RetroLoom/Super-Wave-Blaster/Images/GPM02_MDF/CLK/SP_A_SNES-UN316642987-Toslink_CLK_APU.png

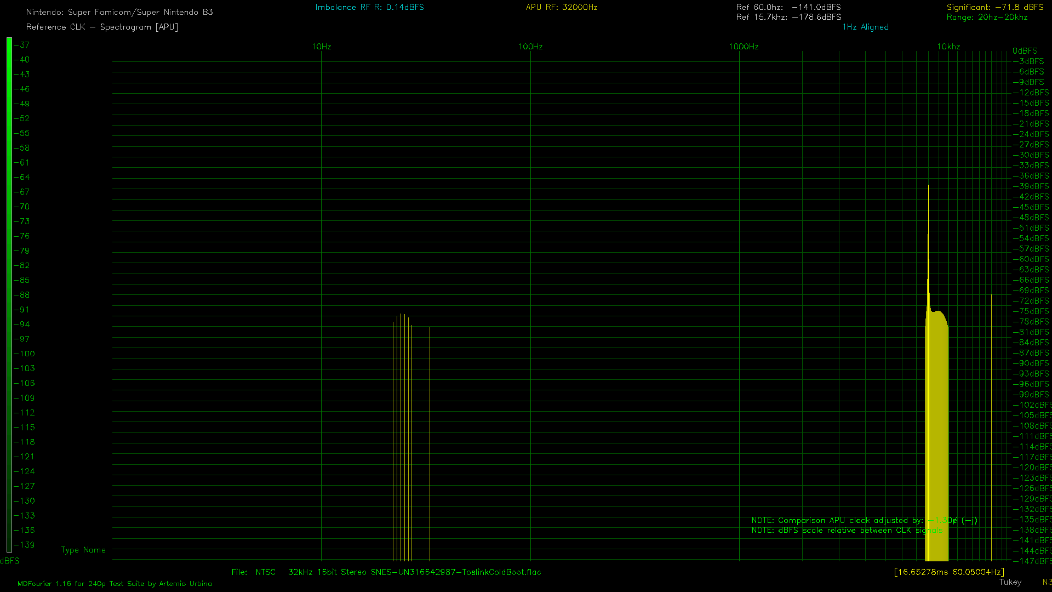
Images/GPM02_MDF/CLK/SP_A_SNES-UN316642987-Toslink_CLK_APU.png
