RetroLoom/Super-Wave-Blaster/Images/GPM02_MDF/CLK/SP_B_SWB GPM02 1UF OPA 44k_CLK_APU.png

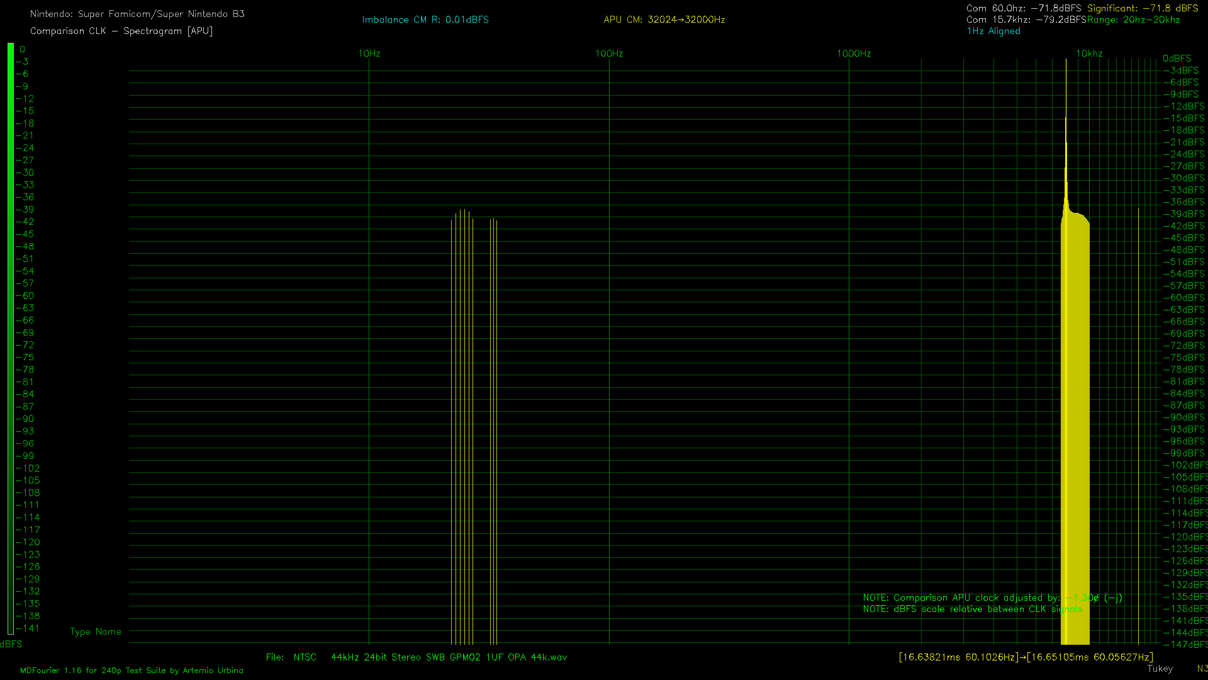
Images/GPM02_MDF/CLK/SP_B_SWB GPM02 1UF OPA 44k_CLK_APU.png
