RetroLoom/Super-Wave-Blaster/Images/GPM02_MDF/MISSING-A-T_SP_SNES-UN316642987-Toslink_S.png

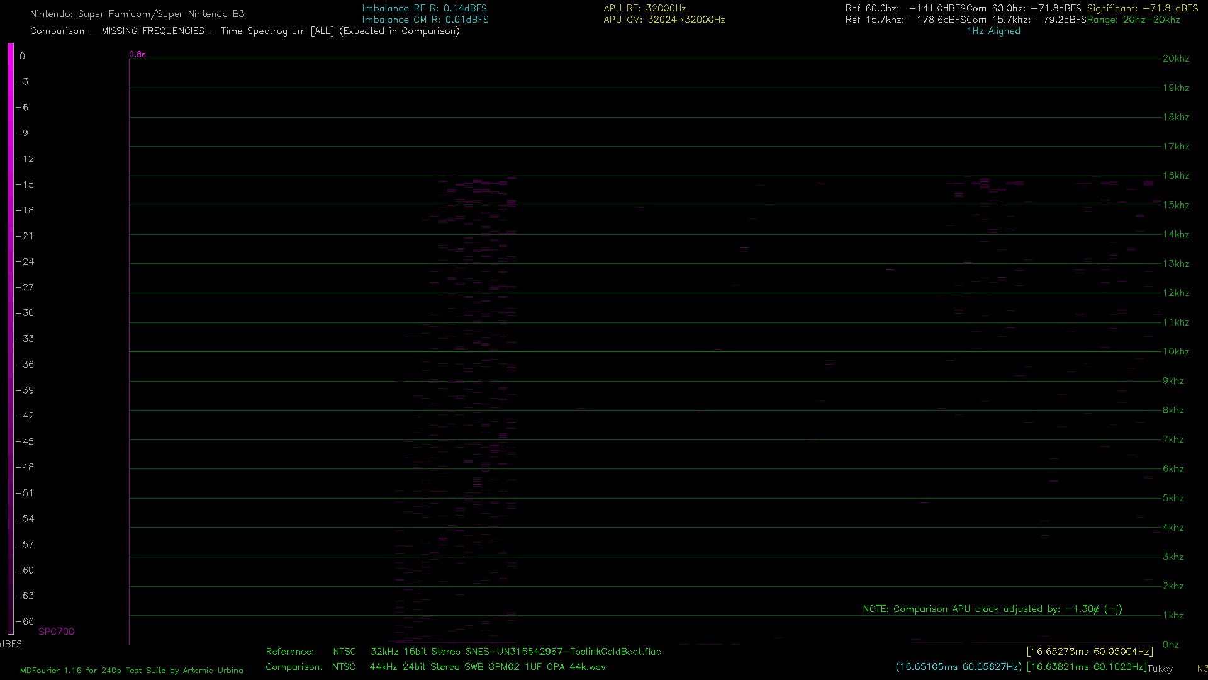
Images/GPM02_MDF/MISSING-A-T_SP_SNES-UN316642987-Toslink_S.png
