RetroLoom/Super-Wave-Blaster/Images/GPM02_MDF/MISSING-EXTRA_T_SP_SWB GPM02 1UF OPA 44k_S.png

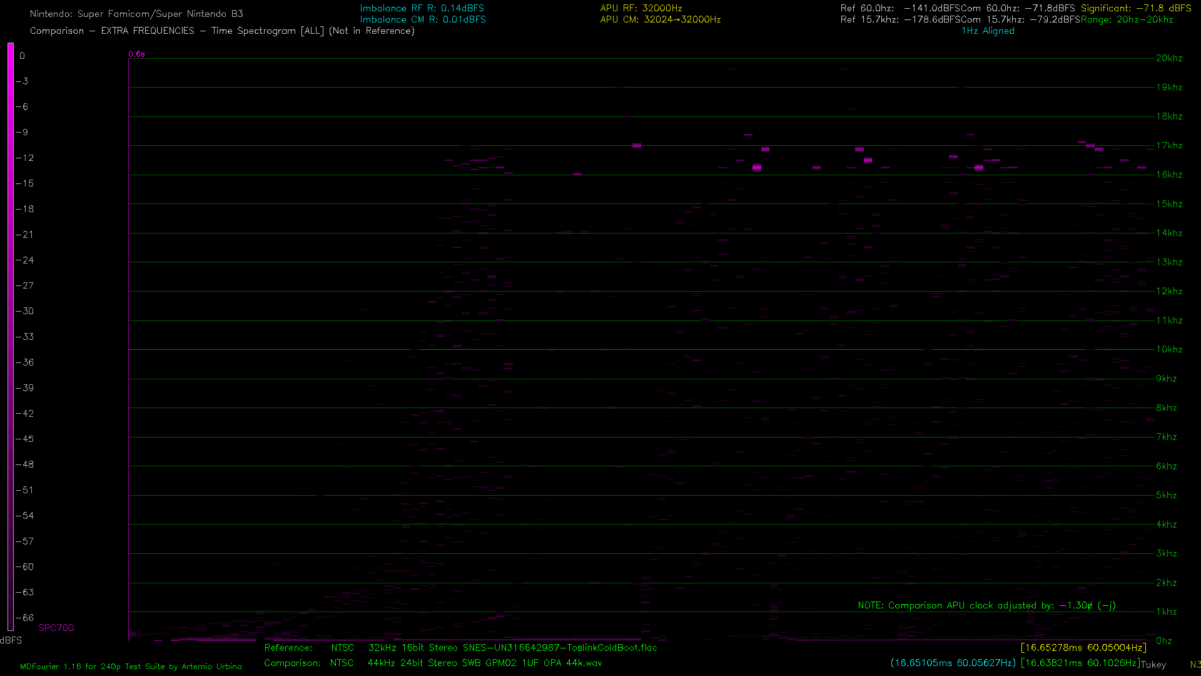
Images/GPM02_MDF/MISSING-EXTRA_T_SP_SWB GPM02 1UF OPA 44k_S.png
