RetroLoom/Super-Wave-Blaster/Images/GPM02_MDF/MissingAndExtra/MISSING-A-T_SP_SNES-UN316642987-Toslink_r.png

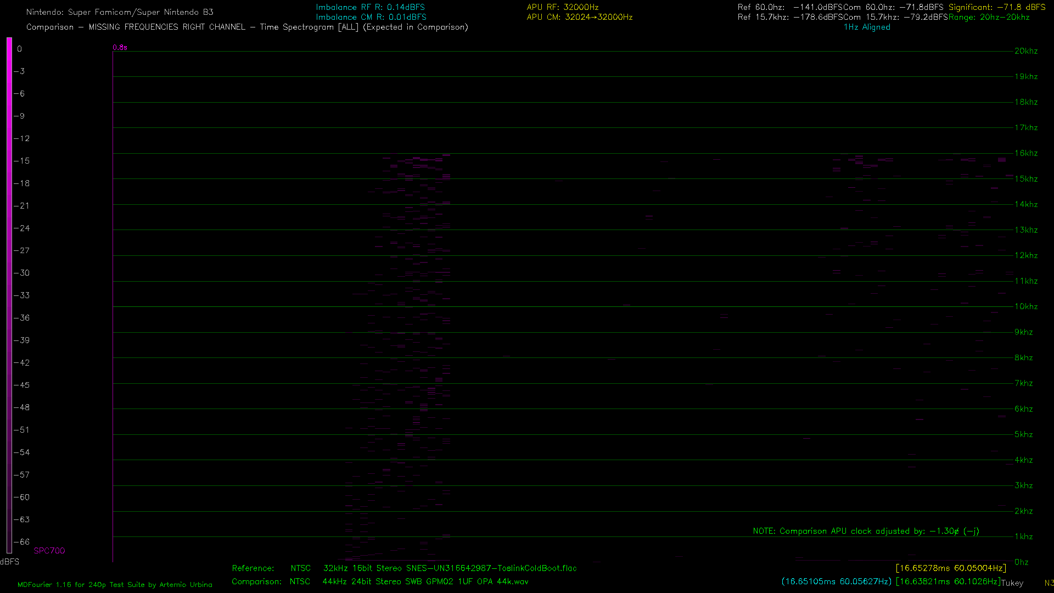
Images/GPM02_MDF/MissingAndExtra/MISSING-A-T_SP_SNES-UN316642987-Toslink_r.png
