RetroLoom/Super-Wave-Blaster/Images/GPM02_MDF/MissingAndExtra/MISSING-EXTRA_T_SP_SWB GPM02 1UF OPA 44k_l.png

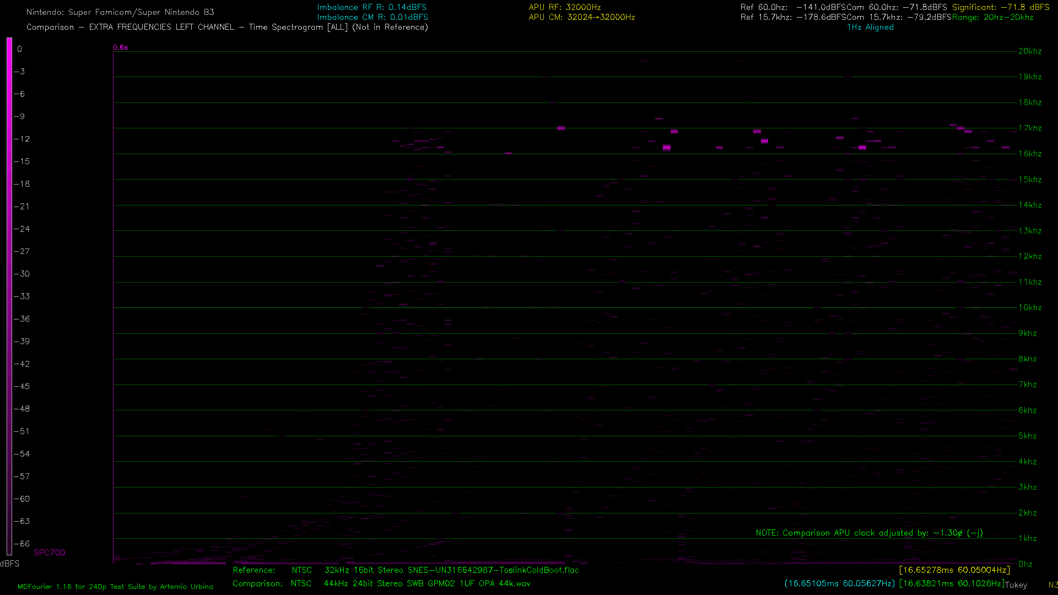
Images/GPM02_MDF/MissingAndExtra/MISSING-EXTRA_T_SP_SWB GPM02 1UF OPA 44k_l.png
