RetroLoom/Super-Wave-Blaster/Images/GPM02_MDF/NF__SNES-UN316642987-Toslink_vs_SWB_GPM02_1UF_OPA_44k_0000_-1Silence_AVG_.png

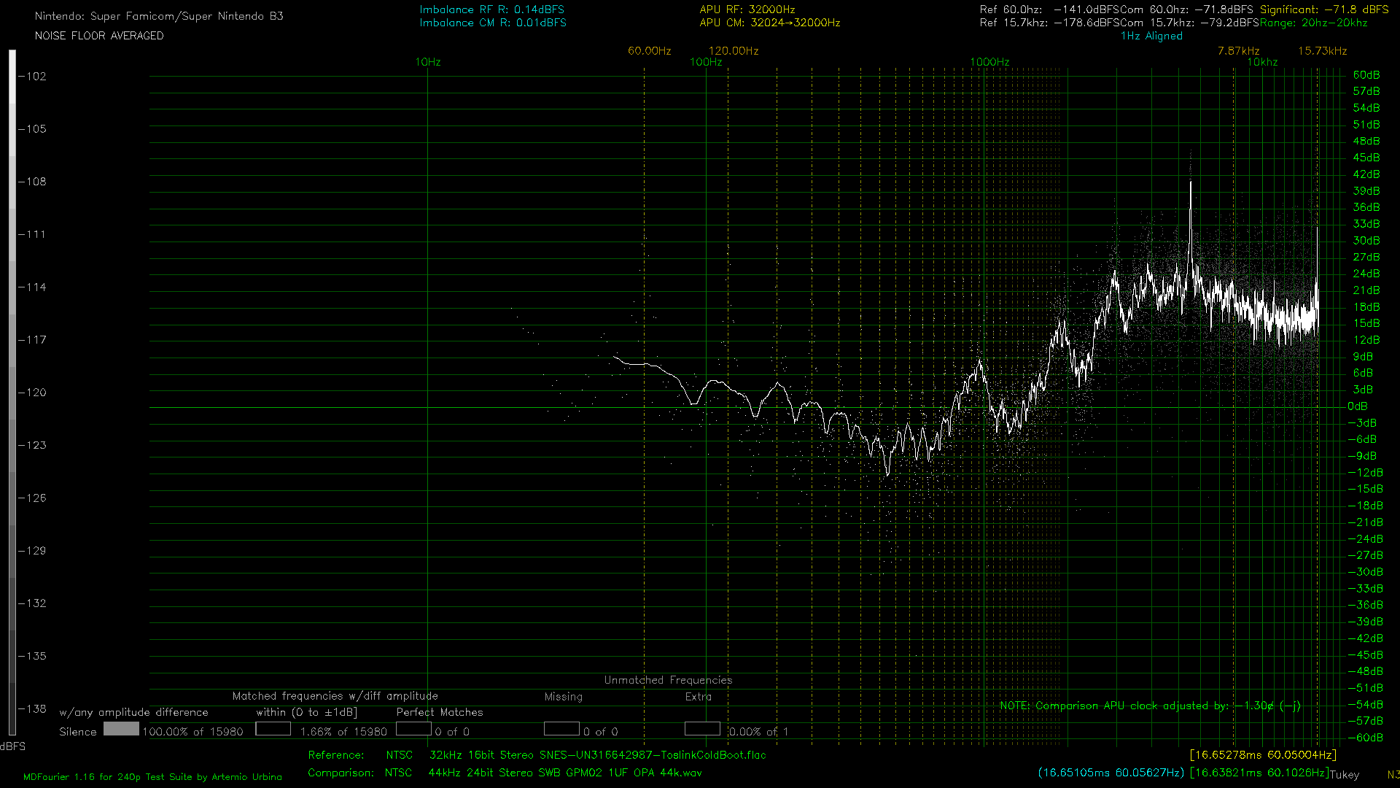
Images/GPM02_MDF/NF__SNES-UN316642987-Toslink_vs_SWB_GPM02_1UF_OPA_44k_0000_-1Silence_AVG_.png
