RetroLoom/Super-Wave-Blaster/Images/GPM02_MDF/NF_SP_A_SNES-UN316642987-Toslink_-1Silence.png

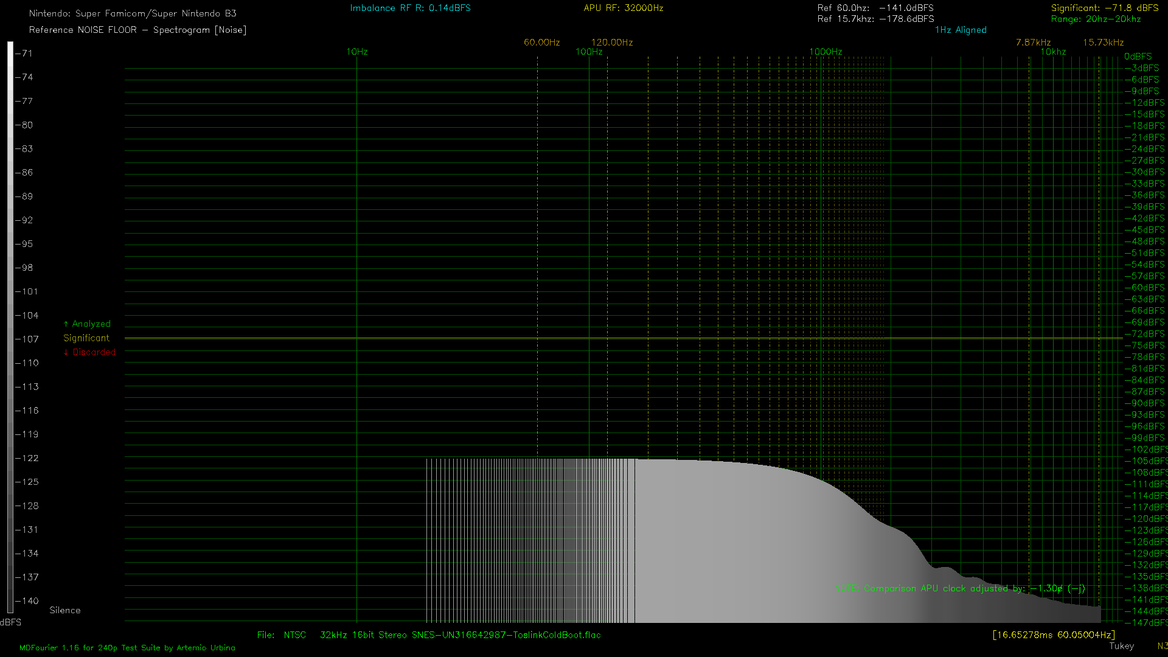
Images/GPM02_MDF/NF_SP_A_SNES-UN316642987-Toslink_-1Silence.png
