RetroLoom/Super-Wave-Blaster/Images/GPM02_MDF/NF_SP_B_SWB GPM02 1UF OPA 44k_-1Silence.png

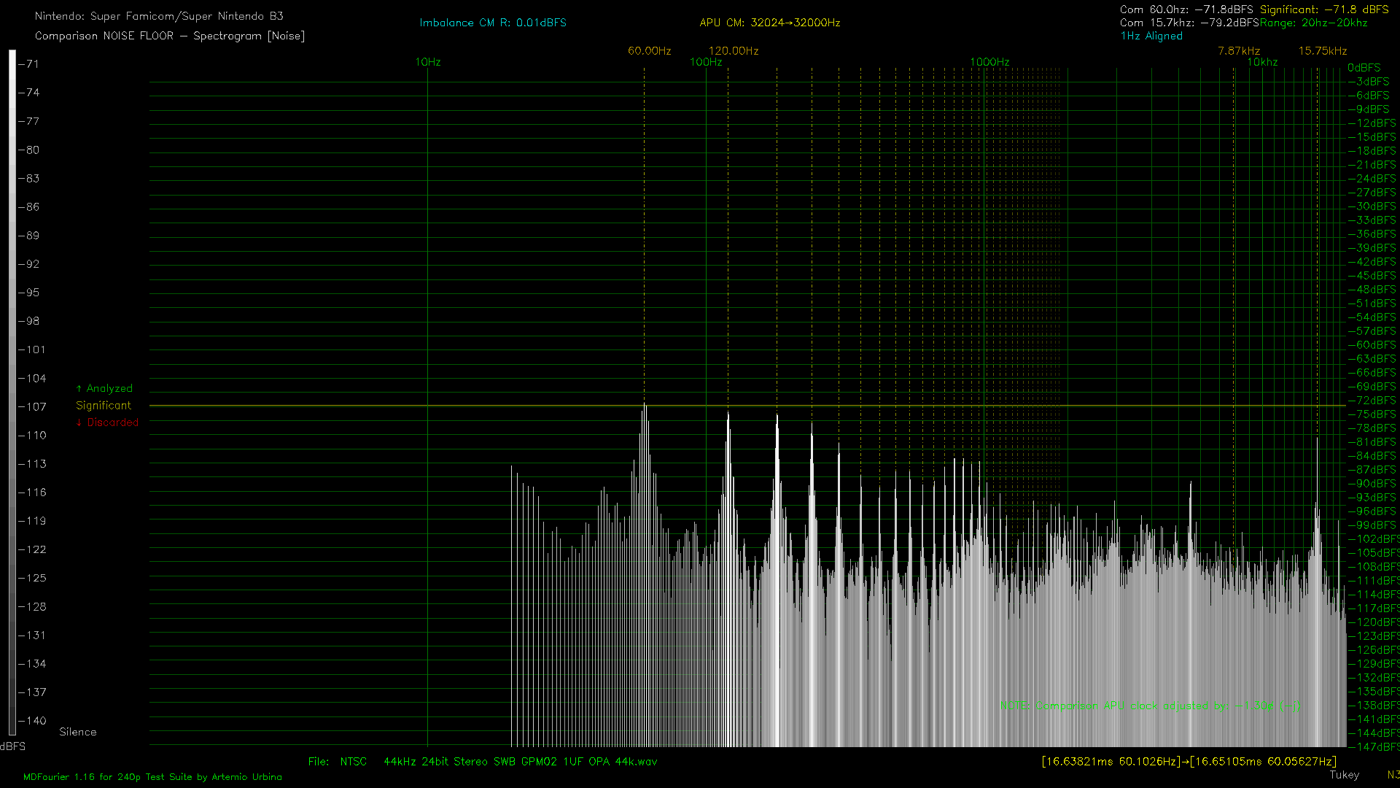
Images/GPM02_MDF/NF_SP_B_SWB GPM02 1UF OPA 44k_-1Silence.png
