RetroLoom/Super-Wave-Blaster/Images/GPM02_MDF/Phase/PHASE_DIFF_SNES-UN316642987-Toslink_vs_SWB_GPM02_1UF_OPA_44k_0000_01SPC700_r.png

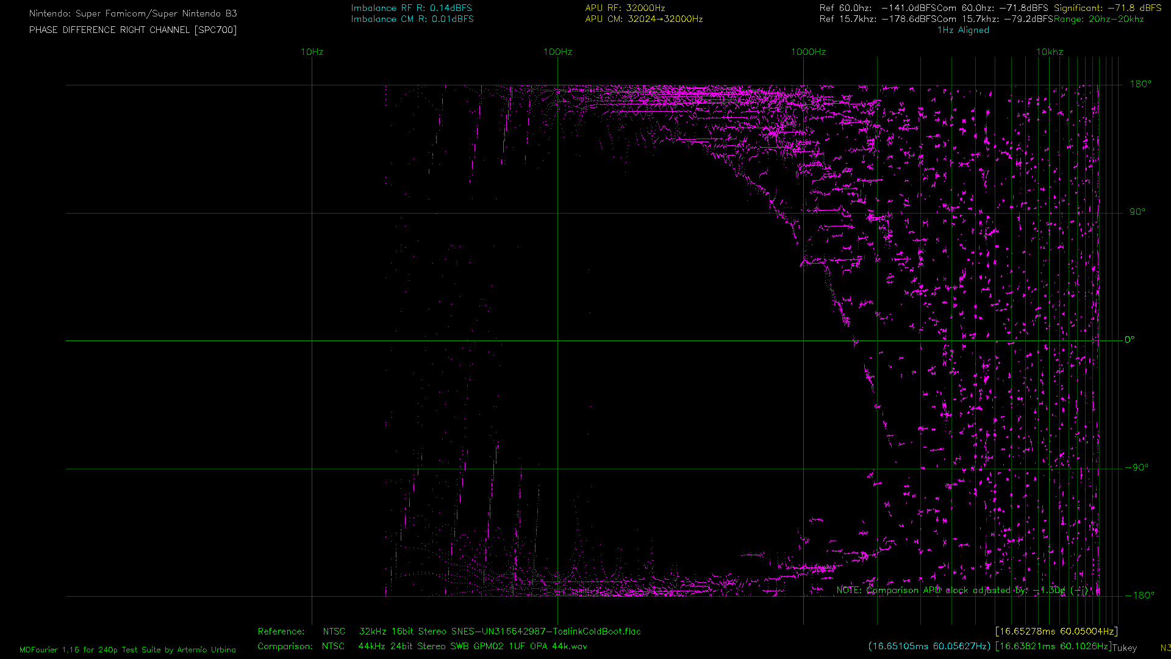
Images/GPM02_MDF/Phase/PHASE_DIFF_SNES-UN316642987-Toslink_vs_SWB_GPM02_1UF_OPA_44k_0000_01SPC700_r.png
