RetroLoom/Super-Wave-Blaster/Images/GPM02_MDF/T_SP_A_SNES-UN316642987-Toslink.png

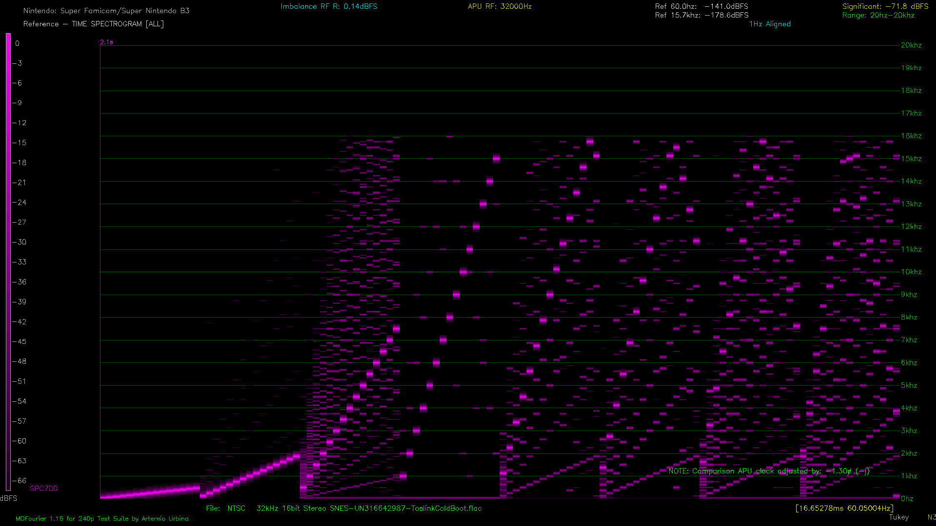
Images/GPM02_MDF/T_SP_A_SNES-UN316642987-Toslink.png
