RetroLoom/Super-Wave-Blaster/Images/GPM02_MDF/T_SP_B_SWB GPM02 1UF OPA 44k.png

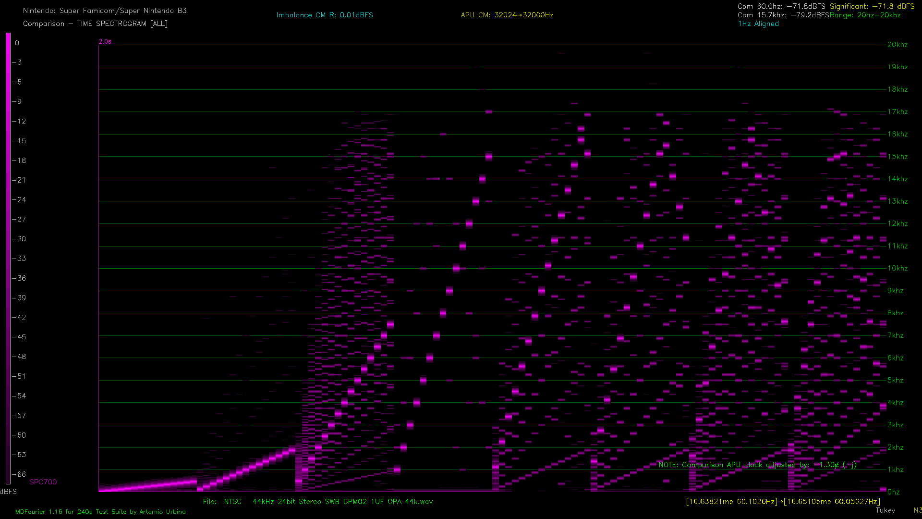
Images/GPM02_MDF/T_SP_B_SWB GPM02 1UF OPA 44k.png
