RetroLoom/Super-Wave-Blaster/Images/GPM02_MDF/TimeSpectrograms/T_SP_r_A_SNES-UN316642987-Toslink.png

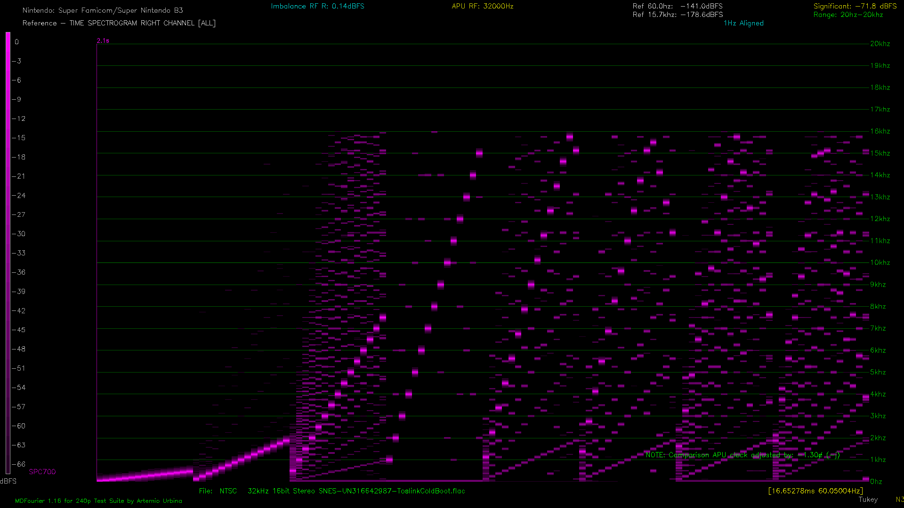
Images/GPM02_MDF/TimeSpectrograms/T_SP_r_A_SNES-UN316642987-Toslink.png
