RetroLoom/Super-Wave-Blaster/Images/GPM02_MDF/Waveforms/TD_00001_3_Silence_00000_SNES-UN316642987-Toslink_vs_SWB_GPM02_1UF_OPA_44k_0000.png

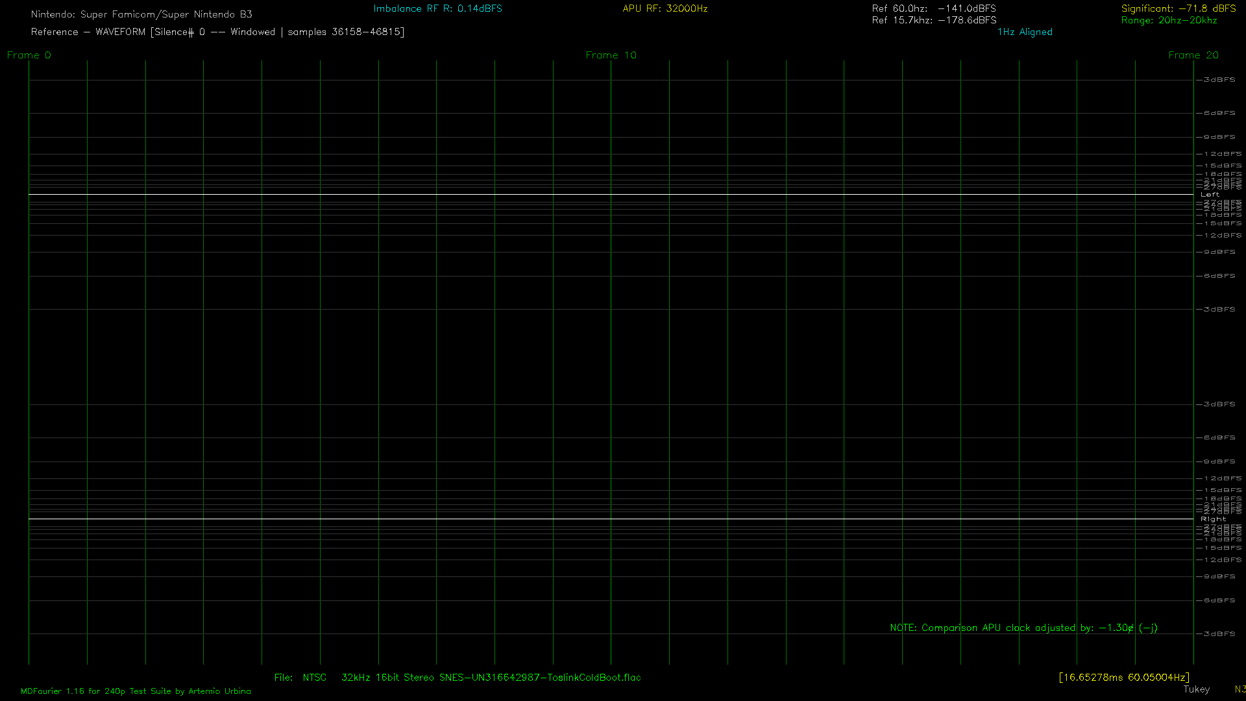
Images/GPM02_MDF/Waveforms/TD_00001_3_Silence_00000_SNES-UN316642987-Toslink_vs_SWB_GPM02_1UF_OPA_44k_0000.png
