RetroLoom/Super-Wave-Blaster/Images/GPM02_MDF/Waveforms/ZOOM_Sync_TD_00000_1_Sync_00000_SNES-UN316642987-Toslink_vs_SWB_GPM02_1UF_OPA_44k_0000.png

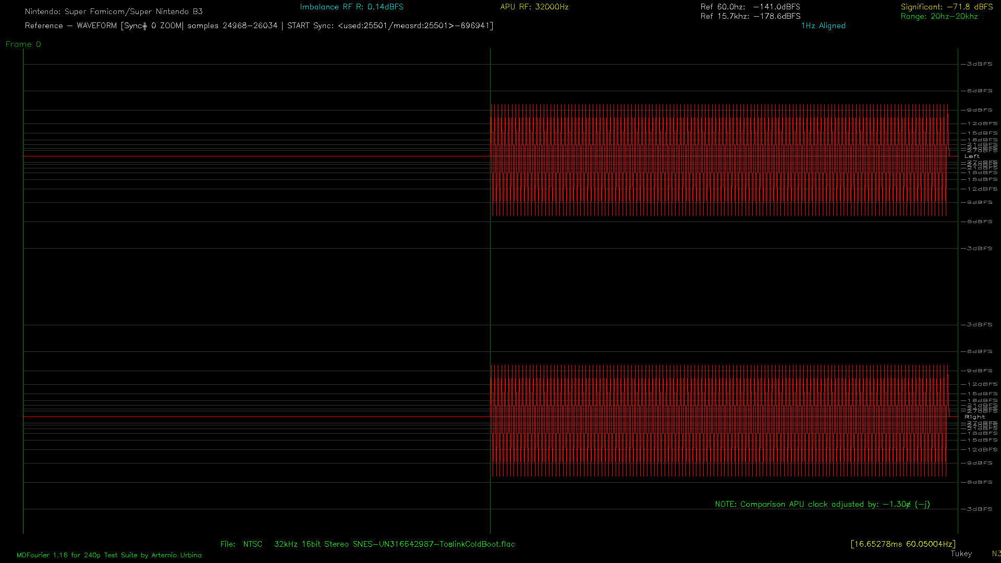
Images/GPM02_MDF/Waveforms/ZOOM_Sync_TD_00000_1_Sync_00000_SNES-UN316642987-Toslink_vs_SWB_GPM02_1UF_OPA_44k_0000.png
